paultimke/Vision_Box/Software/PC_App/set_light.py

import serial
import serial.tools.list_ports
import time
from vbox_logger import logger

LOG_TAG = "SETLIGHT"
class light_controller:
    DELAY_TIME = 2

    def __init__(self):
        """ Light Controller object constructor\
            Establishes serial port connection to MCU """
        self.setup_complete = False

        # Automatically looks for device in listed ports
        # Looks first on last ports as they are more likely
        # to be the light controller device
        ports = serial.tools.list_ports.comports()
        ports.reverse()
        for port in ports:
            try:
                self._ser = serial.Serial(port.device, 
                                         baudrate=38400,
                                         timeout=0.5,
                                         dsrdtr=False,
                                         xonxoff=False)

                # Send dummy byte and wait for response to ensure
                # connection with real light controller device was made
                time.sleep(self.DELAY_TIME)
                DUMMY_BYTES = b'255'
                self._ser.reset_output_buffer()
                self._ser.reset_input_buffer()
                self._ser.write(DUMMY_BYTES)
                if self._wait_mcu_ack(DUMMY_BYTES):
                    self.setup_complete = True
                    logger.debug("VB", f"Connection to {port.device} successful", 
                                 tag=LOG_TAG)
                    break
                else:
                    # If ACK was not received, close connection with
                    # connected serial port
                    self._ser.close()
            except:
                continue
        
        if not self.setup_complete:
            logger.warning("VB", "Could not establish a connection with " 
                  "Light Controller Hardware", tag=LOG_TAG)

    def detach(self):
        """ Light Controller object destructor\
            Closes serial port connection with MCU """
        if self.setup_complete:
            self._ser.close()
            logger.debug("VB", f"Connection with {self._ser.port} closed", 
                         tag=LOG_TAG)

    def set_brightness(self, luxes: int):
        """ Command to set Vision Box light brightness level"""
        if self.setup_complete:
            tx_bytes = self._serialize_luxes(luxes)
            self._ser.reset_output_buffer()
            self._ser.reset_input_buffer()
            self._ser.write(tx_bytes)
            # Confirm data sent was received well
            if self._wait_mcu_ack(tx_bytes):
                logger.info("VB", f"Light brightness succesfully set to {luxes} lux",
                            tag=LOG_TAG)

    def _serialize_luxes(self, luxes: int):
        """ Converts int lux value into corresponding string to be sent\
            prefixed by MCU start char sequence for UART interrupt trigger """
        if self.setup_complete:
            MCU_START_CHAR_SEQUENCE = ""
            tx_bytes = bytearray(MCU_START_CHAR_SEQUENCE + str(luxes), 'utf-8')
            return tx_bytes

    def _wait_mcu_ack(self, compare_string):
        """ Waits for MCU acknowledge to a previously sent command.\n
            Returns True if data received by MCU is equal to data sent
            and False otherwise.
            Data echoed by MCU must match format RX<NL> where X is a number"""
        # Give time for light controller device to respond
        time.sleep(self.DELAY_TIME)

        # Wait for acknowledge and verify data format
        valid = False
        response = self._ser.readline().decode('utf-8')
        if response.startswith('R') and response.endswith('\n'):
            response = response.removeprefix('R').strip()
            if response == compare_string.decode('utf-8'):
                valid = True
        return valid

if __name__ == 'set_light':
    logger.info("VB", 'Initializing serial connection', tag=LOG_TAG)
    light_control = light_controller()

def Set_light(luxes, _):
    light_control.set_brightness(luxes)
